thijstriemstra/garduino/cad/sensors/ring.stl

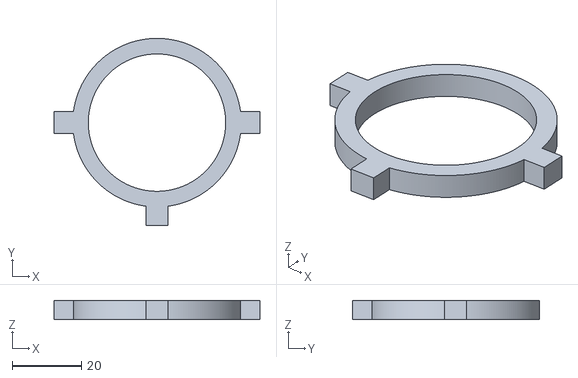
[picture p18: CAD file, 2023-04-06]
cad/sensors/ring.stl
59.4 x 54.0 x 5.50
