thijstriemstra/garduino/cad/plant-label-card.stl

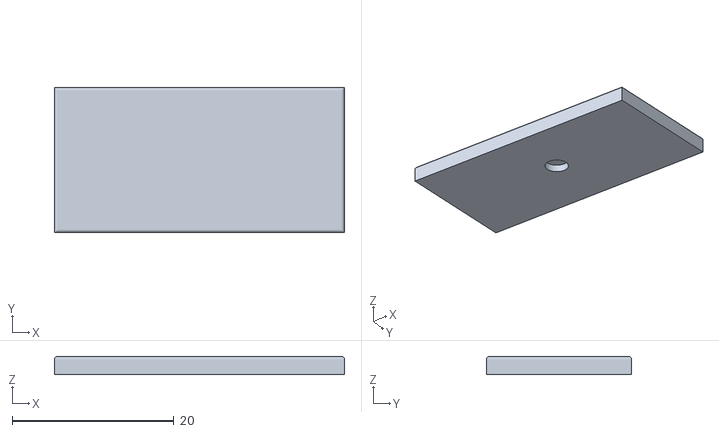
[picture p19: CAD file, 2023-04-06]
cad/plant-label-card.stl
35.8 x 17.9 x 2.25
