thijstriemstra/garduino/cad/sensors/icon-moon.stl

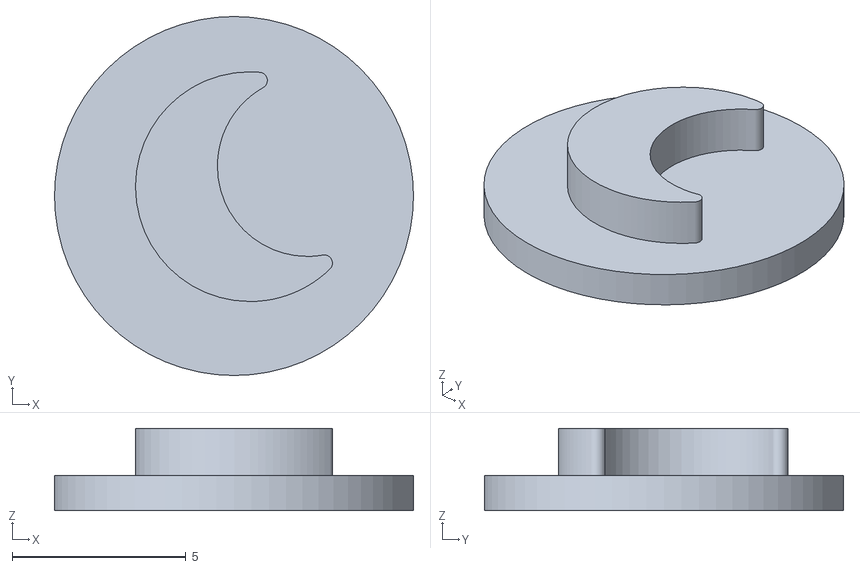
[picture p20: CAD file, 2023-04-06]
cad/sensors/icon-moon.stl
10.3 x 10.3 x 2.37
