thijstriemstra/garduino/cad/handle-right.stl

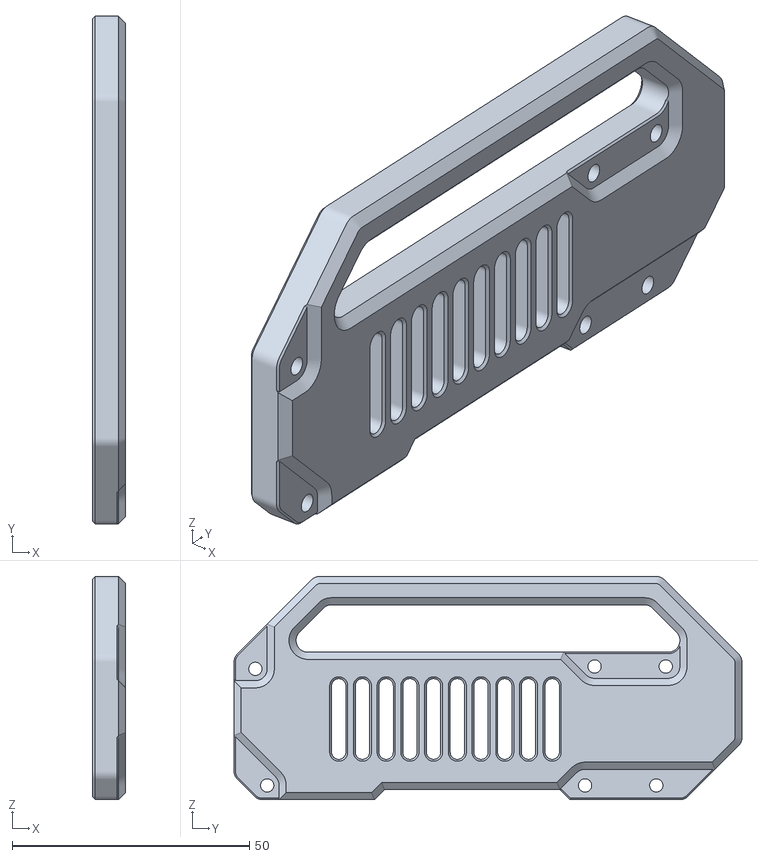
[picture p21: CAD file, 2023-04-06]
cad/handle-right.stl
7.00 x 107.1 x 47.1
