thijstriemstra/garduino/cad/sensors/icon-play.stl

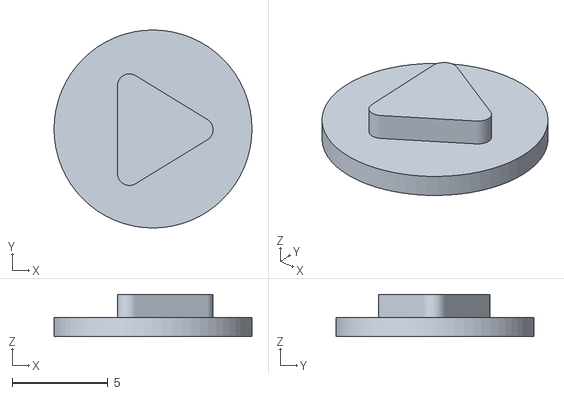
[picture p22: CAD file, 2023-04-06]
cad/sensors/icon-play.stl
10.3 x 10.3 x 2.21
