thijstriemstra/garduino/cad/case-bottom.stl

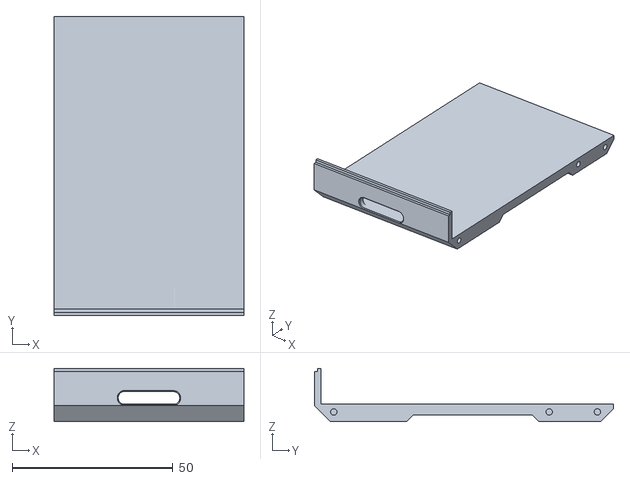
[picture p23: CAD file, 2023-04-06]
cad/case-bottom.stl
59.0 x 93.0 x 16.5
