thijstriemstra/garduino/cad/sensors/door2.stl

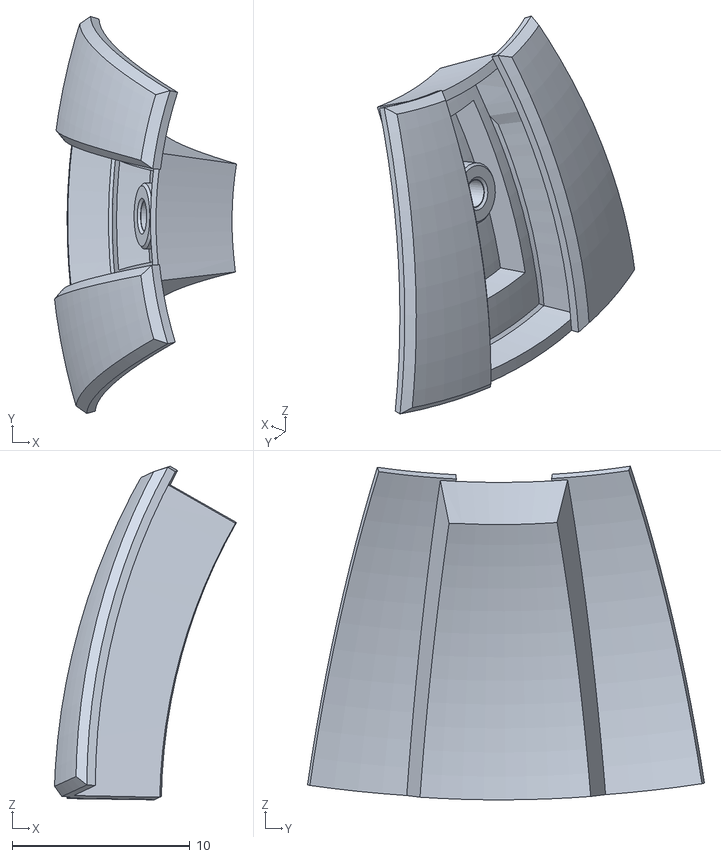
[picture p24: CAD file, 2023-04-06]
cad/sensors/door2.stl
10.3 x 22.4 x 18.8
