thijstriemstra/garduino/cad/conn-6-pin-cover.stl

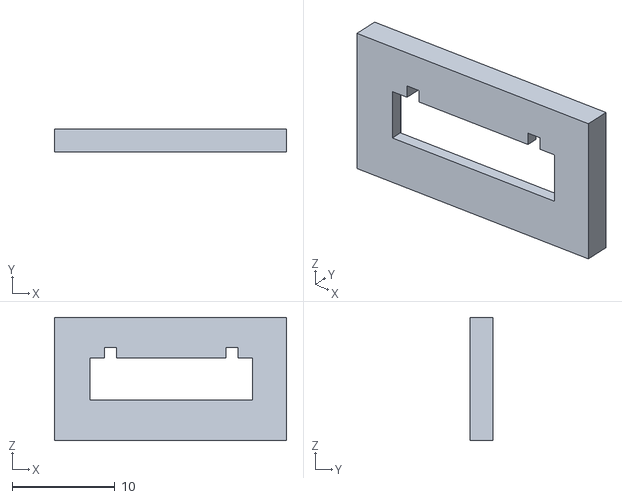
[picture p25: CAD file, 2023-04-06]
cad/conn-6-pin-cover.stl
22.6 x 2.20 x 12.0
