thijstriemstra/garduino/cad/sensors/icon-power.stl

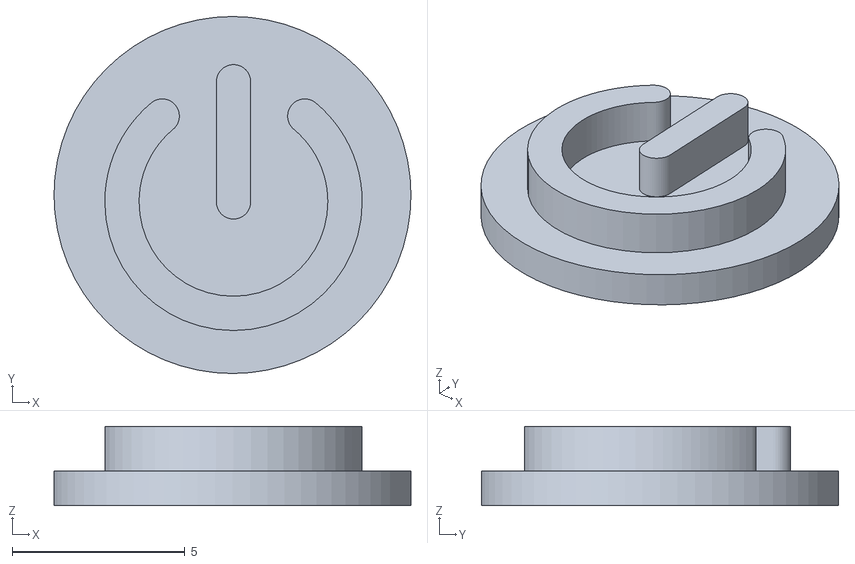
[picture p26: CAD file, 2023-04-06]
cad/sensors/icon-power.stl
10.3 x 10.3 x 2.29
