thijstriemstra/garduino/cad/sensors/thrusters.stl

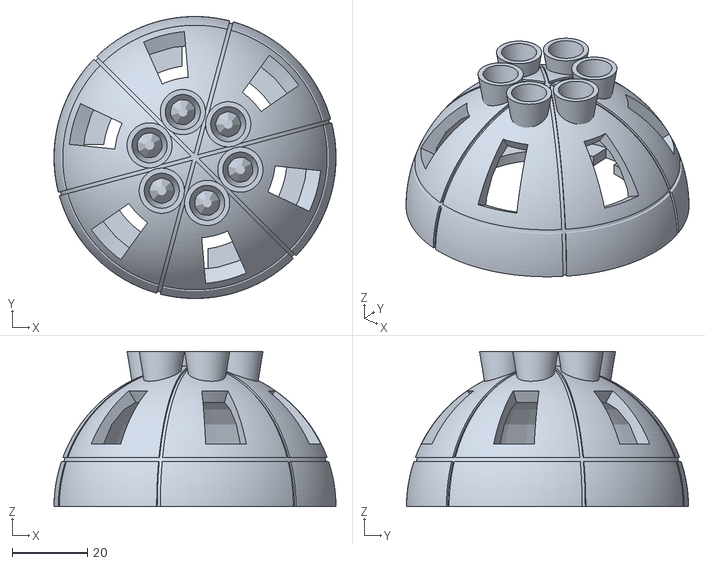
[picture p27: CAD file, 2023-04-06]
cad/sensors/thrusters.stl
75.0 x 75.0 x 41.2
