thijstriemstra/garduino/cad/Top Shell.stl

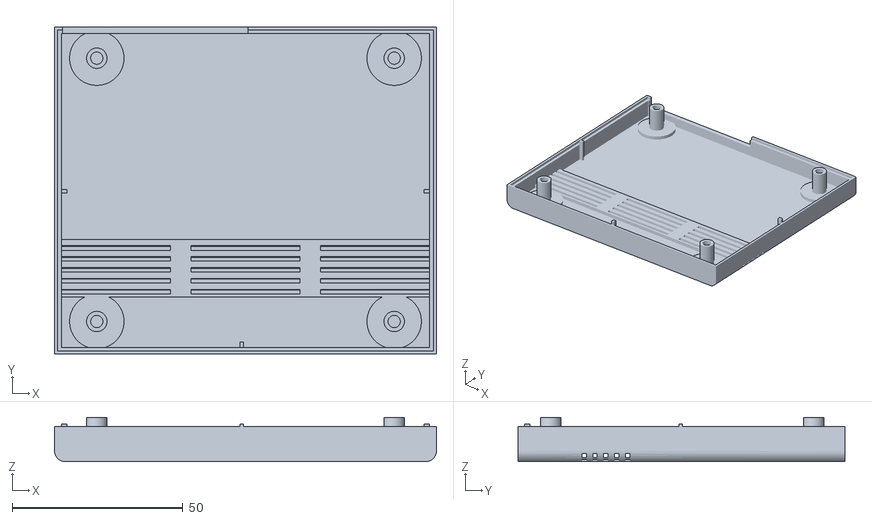
[picture p28: CAD file, 2023-04-06]
cad/Top Shell.stl
112.0 x 96.0 x 13.0
