thijstriemstra/garduino/cad/sensors/ctrl-panel-button-cap.stl

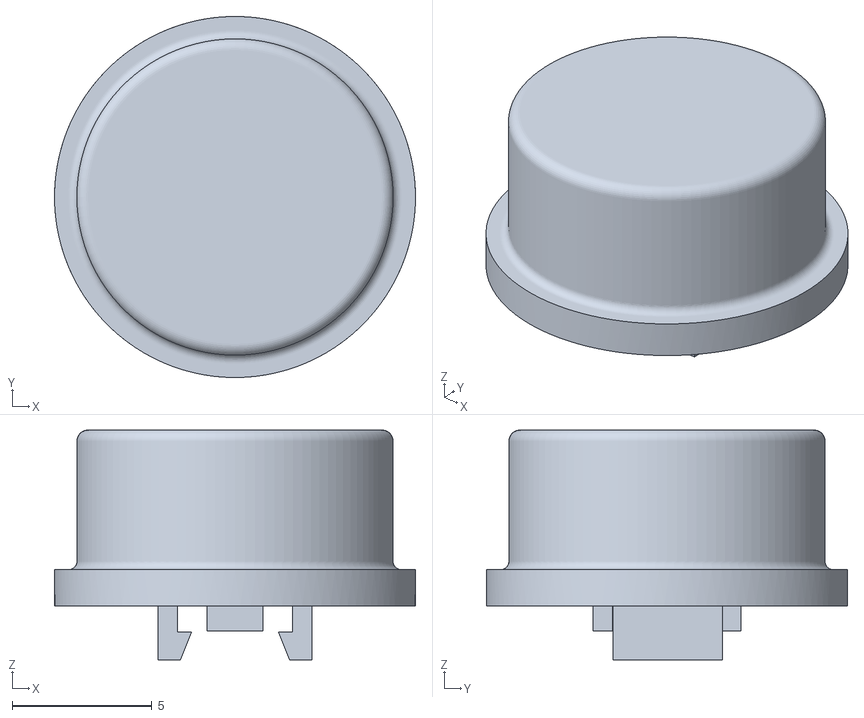
[picture p29: CAD file, 2023-04-06]
cad/sensors/ctrl-panel-button-cap.stl
12.9 x 12.9 x 8.22
