thijstriemstra/garduino/cad/tsl2591-light-sensor.stl

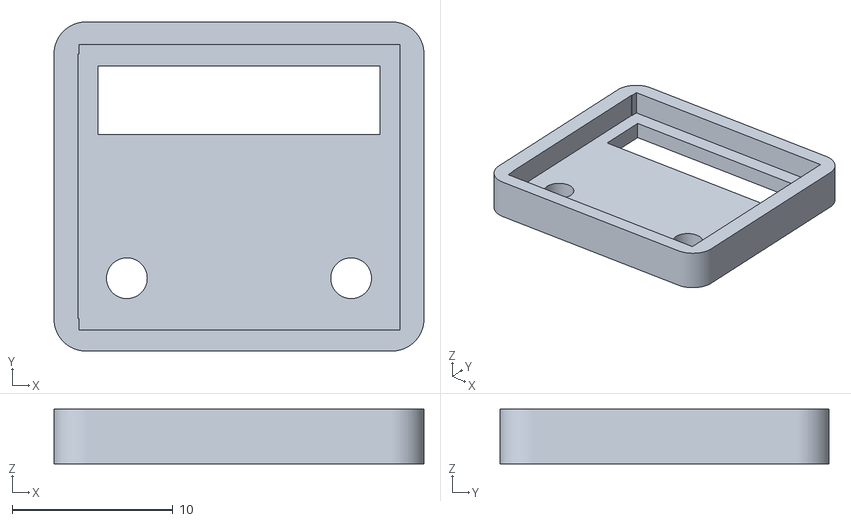
[picture p30: CAD file, 2023-04-06]
cad/tsl2591-light-sensor.stl
23.0 x 20.5 x 3.40
