thijstriemstra/garduino/cad/buck-converter-bottom.stl

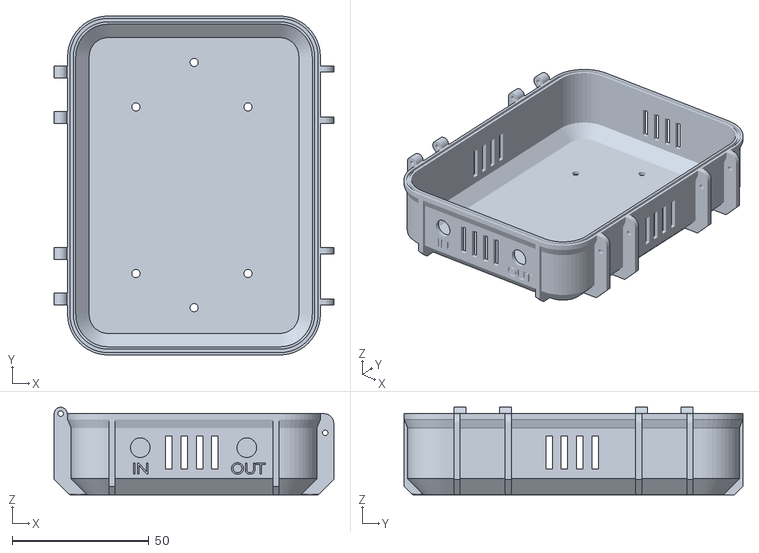
[picture p31: CAD file, 2023-04-06]
cad/buck-converter-bottom.stl
102.3 x 124.0 x 32.1
