thijstriemstra/garduino/cad/sensors/ctrl-panel-front.stl

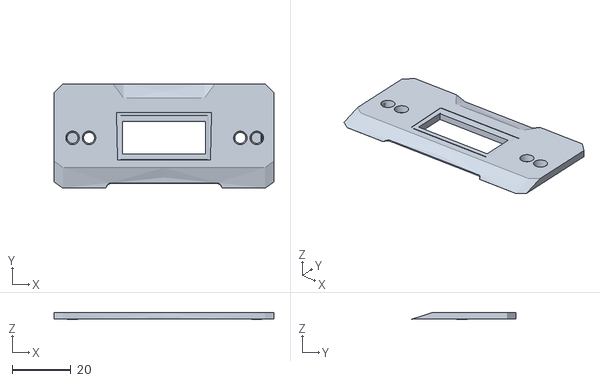
[picture p32: CAD file, 2023-04-06]
cad/sensors/ctrl-panel-front.stl
75.0 x 35.4 x 2.46
