thijstriemstra/garduino/cad/Bottom Connectors.stl

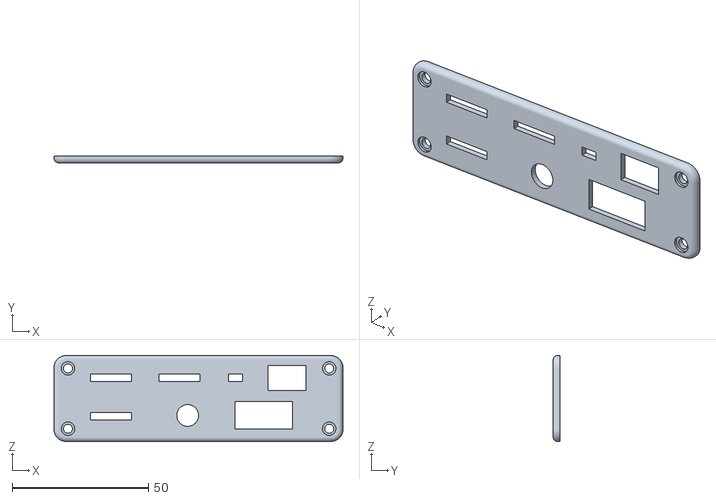
[picture p33: CAD file, 2023-04-06]
cad/Bottom Connectors.stl
106.0 x 2.44 x 31.5
