thijstriemstra/garduino/cad/sensors/ctrl-panel-top.stl

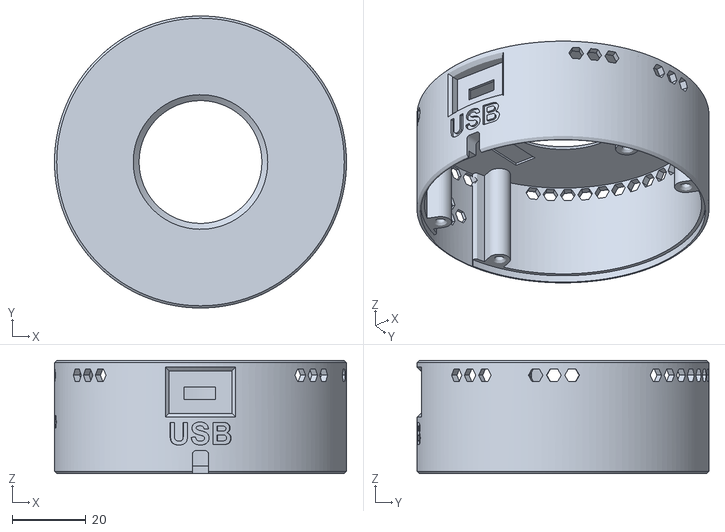
[picture p34: CAD file, 2023-04-06]
cad/sensors/ctrl-panel-top.stl
79.0 x 79.0 x 30.6
