thijstriemstra/garduino/cad/bme280-holder.stl

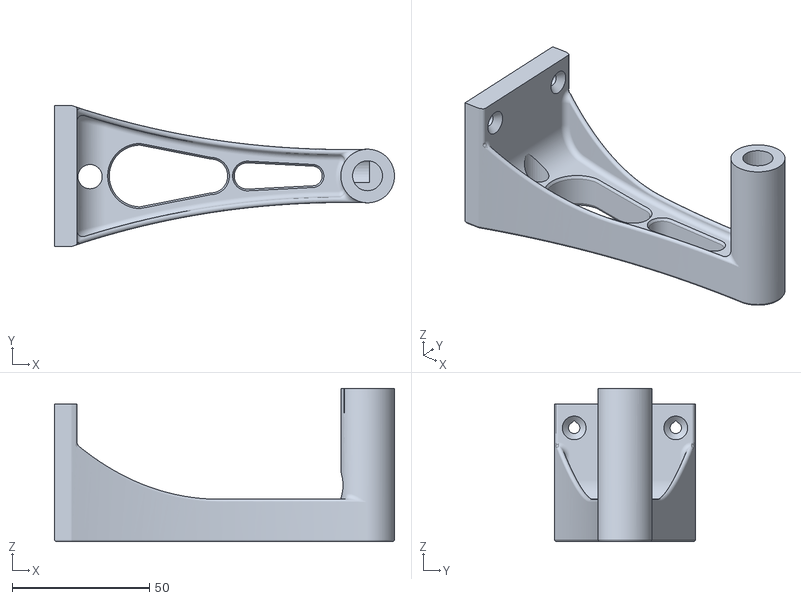
[picture p35: CAD file, 2023-04-06]
cad/bme280-holder.stl
124.1 x 51.5 x 55.9
