thijstriemstra/garduino/cad/sensors/case-top.stl

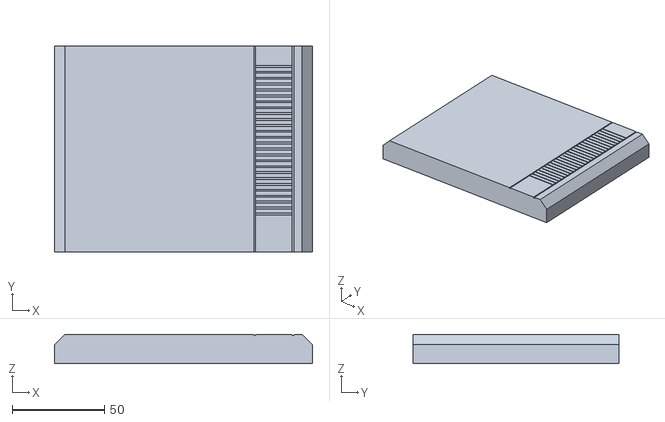
[picture p36: CAD file, 2023-04-06]
cad/sensors/case-top.stl
140.0 x 112.0 x 16.0
