thijstriemstra/garduino/cad/bme280-top.stl

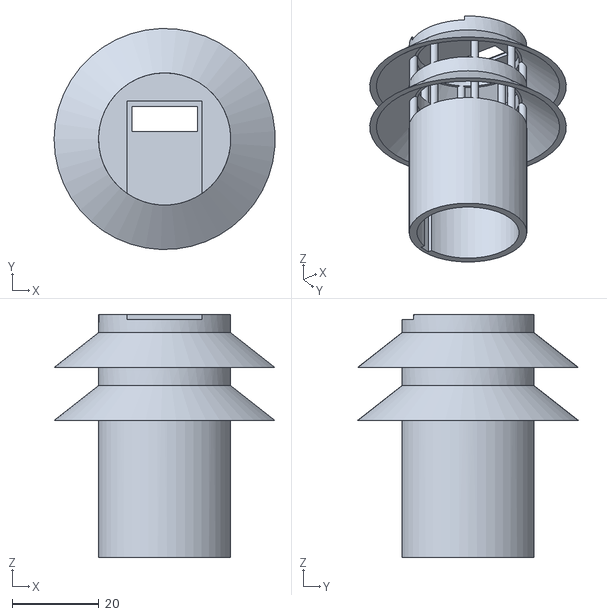
[picture p37: CAD file, 2023-04-06]
cad/bme280-top.stl
50.9 x 51.0 x 56.0
