thijstriemstra/garduino/cad/sensors/case-bottom.stl

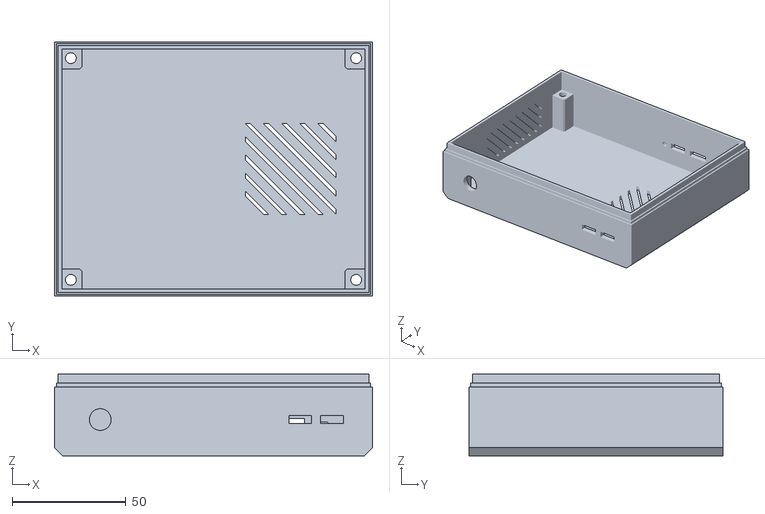
[picture p38: CAD file, 2023-04-06]
cad/sensors/case-bottom.stl
140.0 x 112.0 x 36.0
