thijstriemstra/garduino/cad/case-top.stl

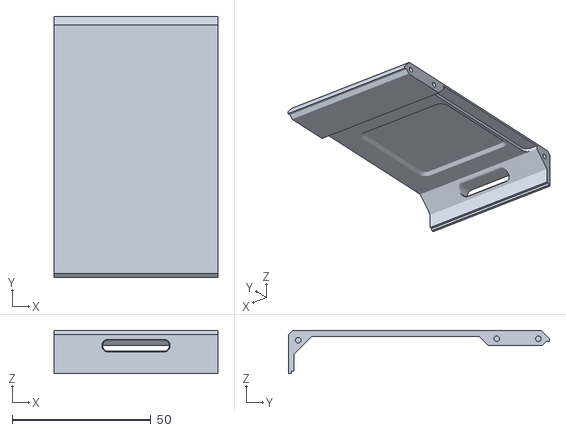
[picture p39: CAD file, 2023-04-06]
cad/case-top.stl
59.0 x 94.0 x 15.5
