thijstriemstra/garduino/cad/sensors/ctrl-panel-description.stl

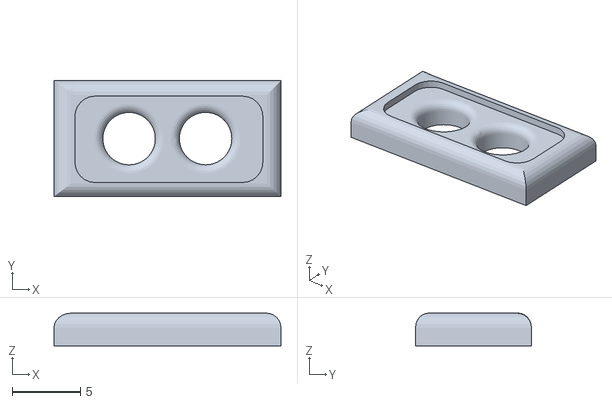
[picture p40: CAD file, 2023-04-06]
cad/sensors/ctrl-panel-description.stl
16.6 x 8.50 x 2.40
