thijstriemstra/garduino/cad/Bottom Shell PCB only.stl

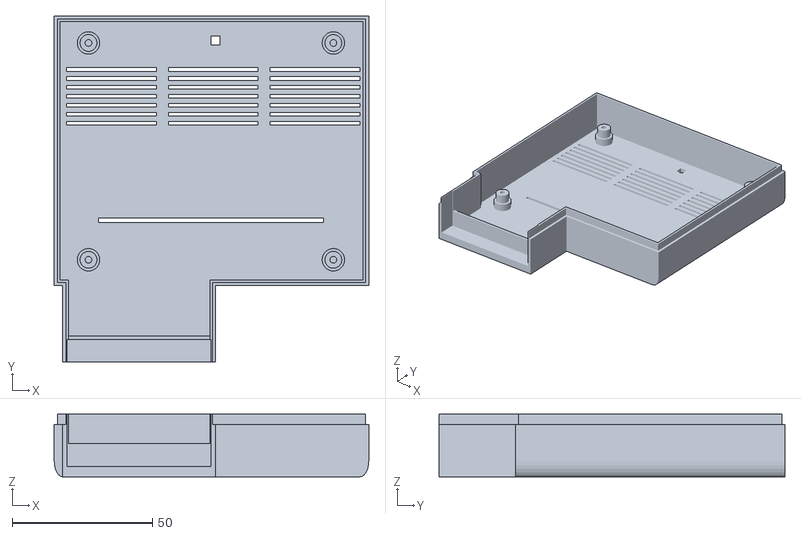
[picture p41: CAD file, 2023-04-06]
cad/Bottom Shell PCB only.stl
112.0 x 123.2 x 22.4
