thijstriemstra/garduino/cad/buck-converter-top.stl

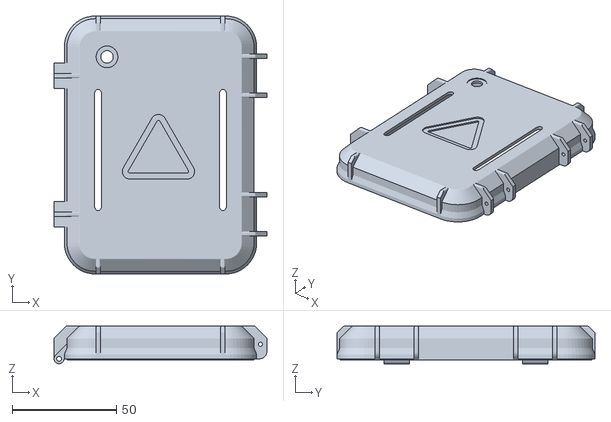
[picture p42: CAD file, 2022-04-19]
cad/buck-converter-top.stl
102.3 x 124.0 x 18.1
