thijstriemstra/garduino/cad/buck-converter-icon.stl

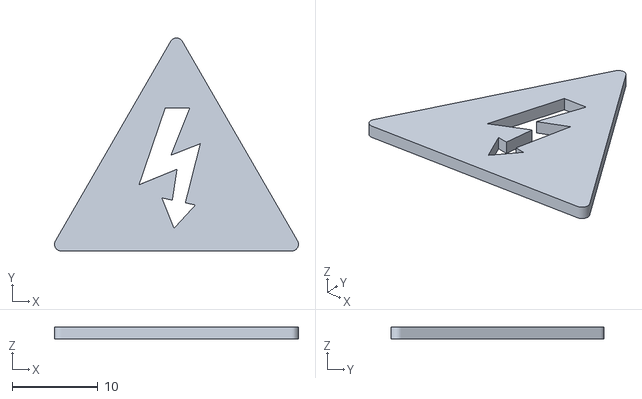
[picture p43: CAD file, 2022-04-19]
cad/buck-converter-icon.stl
28.5 x 24.9 x 1.35
