thijstriemstra/garduino/cad/buck-converter-latch.stl

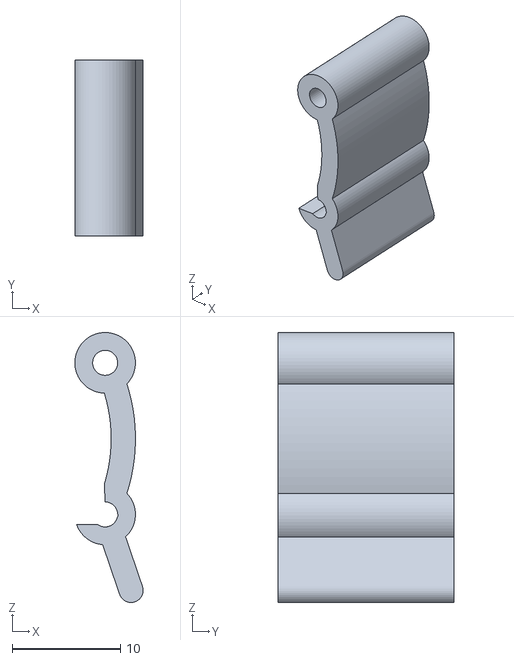
[picture p44: CAD file, 2022-04-15]
cad/buck-converter-latch.stl
6.31 x 16.2 x 24.9
