thijstriemstra/garduino/include/Sensors.h

/*  Copyright (c) 2020-2023, Collab
 *  All rights reserved
*/
/*
  Sensors.h
*/
#ifndef Sensors_h
#define Sensors_h

#include <Arduino.h>
#include <ArduinoLog.h>

#include <IOT.h>
#include <SoilSensors.h>
#include <MultiPlexer_MCP3008.h>
#include <MultiPlexer_TCA9548A.h>
#include <TSL2591_LightSensor_Mux.h>
#include <BME280_BarometerSensor_Mux.h>
#include <DS18B20_TemperatureSensors.h>

struct OutsideTemperatureResult {
    float air;
    float water;
};

class Sensors {
  public:
    Sensors(
      long interval_period,
      MultiPlexer_TCA9548A* i2c,
      TwoWire* wire,
      bool debug = true,
      const char *ns = "garduino"
    );
    void begin();
    void run();
    void save();
    void wait();
    void reset();
    void publish();
    int measureRain();
    void startPublish(IOT* iot, float system_temperature);
    float measureLight(bool debug = false);
    BME280_Result readBarometer(bool debug = false);
    OutsideTemperatureResult readOutsideTemperature();
    SoilMoistureResult readSoilMoisture(bool debug = false, bool percentage = false);

    IOT* _iot;
    unsigned long interval;
    bool manualMode = false;

  private:
    bool _debug;
    float _sysTemperature = 0;

    static void setupTask(void *pvParameter);

    TwoWire *_wire;
    SoilSensors* _soil;
    MultiPlexer_MCP3008* _adc;
    TSL2591_LightSensor_Mux* _light;
    BME280_BarometerSensor_Mux* _barometer;
    DS18B20_TemperatureSensors* _temperature;
};

#endif
