thijstriemstra/garduino/include/PowerManagement.h

/*  Copyright (c) 2020-2023, Collab
 *  All rights reserved
*/
/*
   PowerManagement.h
*/
#ifndef PowerManagement_h
#define PowerManagement_h

#include <Arduino.h>
#include <Method.h>
#include <ArduinoLog.h>

/* Conversion factor for micro seconds to seconds */
#define uS_TO_S_FACTOR 1000000

class PowerManagement
{
  public:
    PowerManagement(int wakeupPin, int wakeupTime = 20);
    void init(Method wakeup_callback);
    void sleep();
    void wokeup();

    esp_sleep_wakeup_cause_t wakeup_reason;

  private:
    Method _wakeupCallback;
    int _wakeupPin;
    int _wakeupTime;
};

#endif
