thijstriemstra/garduino/include/images.h

/*  Copyright (c) 2023, Collab
 *  All rights reserved
*/

#ifndef images_h
#define images_h

// https://fontawesome.com/icons/clock
#include "../images/clock.xbm"

// https://fontawesome.com/icons/droplet
#include "../images/droplet.xbm"

// https://fontawesome.com/icons/shower
#include "../images/shower.xbm"

// https://fontawesome.com/icons/sun
#include "../images/sun.xbm"

// https://fontawesome.com/icons/cloud
#include "../images/cloud.xbm"

// https://fontawesome.com/icons/moon
#include "../images/moon.xbm"

// https://www.flaticon.com/free-icons/plant
#include "../images/soil.xbm"

// https://fontawesome.com/icons/calendar-days
#include "../images/calendar-days.xbm"

// https://fontawesome.com/icons/circle
#include "../images/circle.xbm"

// https://fontawesome.com/icons/circle-check
#include "../images/circle-check.xbm"

// https://pictogrammers.com/library/mdi
#include "../images/greenhouse.xbm"
#include "../images/wifi-strength-alert.xbm"
#include "../images/wifi-strength-1.xbm"
#include "../images/wifi-strength-2.xbm"
#include "../images/wifi-strength-3.xbm"
#include "../images/wifi-strength-4.xbm"
#include "../images/numeric-1-circle.xbm"
#include "../images/numeric-2-circle.xbm"
#include "../images/numeric-3-circle.xbm"
#include "../images/numeric-4-circle.xbm"
#include "../images/numeric-5-circle.xbm"
#include "../images/numeric-6-circle.xbm"
#include "../images/numeric-7-circle.xbm"
#include "../images/numeric-8-circle.xbm"

// Font: Antihero
#include "../images/logo.xbm"

#endif
